jeffreyer/Bottle/src/text.cpp

#include "text.h"
#include <Arduino.h>
#include <stdio.h>
#include "common.h"
#include "esp_partition.h"

uint8_t text[] = {'H','e','l','l','o','1','2','3',0xCF, 0xC8, 0xB5, 0xDB, 0xB4, 0xB4, 0xD2, 0xB5, 0xCE, 0xB4, 0xB0, 0xEB, 0xB6, 0xF8, 0xD6, 0xD0, 0xB5, 0xC0, 0xB1, 0xC0, 0xE9, 0xE3, 0xA3, 0xAC, 0xBD, 0xF1, 0xCC, 0xEC, 0xCF, 0xC2, 0xC8, 0xFD, 0xB7, 0xD6, 0xA3, 0xAC, 0xD2, 0xE6, 0xD6, 0xDD, 0xC6, 0xA3, 0xB1, 0xD7, 0xA3, 0xAC, 0xB4, 0xCB, 0xB3, 0xCF, 0xCE, 0xA3, 0xBC, 0xB1, 0xB4, 0xE6, 0xCD, 0xF6, 0xD6, 0xAE, 0xC7, 0xEF, 0xD2, 0xB2, 0xA1, 0xA3, 0xC8, 0xBB, 0xCA, 0xCC, 0xCE, 0xC0, 0xD6, 0xAE, 0xB3, 0xBC, 0xB2, 0xBB, 0xD0, 0xB8, 0xD3, 0xDA, 0xC4, 0xDA, 0xA3, 0xAC, 0xD6, 0xD2, 0xD6, 0xBE, 0xD6, 0xAE, 0xCA, 0xBF, 0xCD, 0xFC, 0xC9, 0xED, 0xD3, 0xDA, 0xCD, 0xE2, 0xD5, 0xDF, 0xA3, 0xAC, 0xB8, 0xC7, 0xD7, 0xB7, 0xCF, 0xC8, 0xB5, 0xDB, 0xD6, 0xAE, 0xCA, 0xE2, 0xD3, 0xF6, 0xA3, 0xAC, 0xD3, 0xFB, 0xB1, 0xA8, 0xD6, 0xAE, 0xD3, 0xDA, 0xB1, 0xDD, 0xCF, 0xC2, 0xD2, 0xB2, 0xA1, 0xA3, 0xB3, 0xCF, 0xD2, 0xCB, 0xBF, 0xAA, 0xD5, 0xC5, 0xCA, 0xA5, 0xCC, 0xFD, 0xA3, 0xAC, 0xD2, 0xD4, 0xB9, 0xE2, 0xCF, 0xC8, 0xB5, 0xDB, 0xD2, 0xC5, 0xB5, 0xC2, 0xA3, 0xAC, 0xBB, 0xD6, 0xBA, 0xEB, 0xD6, 0xBE, 0xCA, 0xBF, 0xD6, 0xAE, 0xC6, 0xF8, 0xA3, 0xAC, 0xB2, 0xBB, 0xD2, 0xCB, 0xCD, 0xFD, 0xD7, 0xD4, 0xB7, 0xC6, 0xB1, 0xA1, 0xA3, 0xAC, 0xD2, 0xFD, 0xD3, 0xF7, 0xCA, 0xA7, 0xD2, 0xE5, 0xA3, 0xAC, 0xD2, 0xD4, 0xC8, 0xFB, 0xD6, 0xD2, 0xDA, 0xC9, 0xD6, 0xAE, 0xC2, 0xB7, 0xD2, 0xB2, 0xA1, 0xA3, 0x0A, 0xB9, 0xAC, 0xD6, 0xD0, 0xB8, 0xAE, 0xD6, 0xD0, 0xA3, 0xAC, 0xBE, 0xE3, 0xCE, 0xAA, 0xD2, 0xBB, 0xCC, 0xE5, 0xA3, 0xBB, 0xDA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
int text_index=0;
bool single_finish=true;
uint8_t *last_glyph;

int gb2312_to_index(uint8_t high, uint8_t low)
{
    if (high==0)
        return low-0x20;
    if (high >= 0xB0 && high <= 0xD7) {
        return (high - 0xB0) * 94 + (low - 0xA1) + 95;
    }
    if (high >= 0xD8 && high <= 0xF7) {
        return (high - 0xD8 + 40) * 94 + (low - 0xA1) + 95;
    }
    return -1;
}

#define FONT_BASE_ADDR 0x390000
#define FONT_PAGE_SIZE (256 * 8)   // 256字/页 × 8 bytes
#define PAGE_CHAR_COUNT 256

typedef struct {
    uint16_t page_id;
    uint8_t data[PAGE_CHAR_COUNT * 8];
    bool valid;
} font_page_t;

font_page_t cache[2];  // 双页缓存

const esp_partition_t* font_part;

void init_font_partition()
{
    font_part = esp_partition_find_first(
        ESP_PARTITION_TYPE_DATA,
        ESP_PARTITION_SUBTYPE_ANY,
        "font"
    );

    if (!font_part) {
        Serial.println("Font partition not found!");
    }
}

bool font_read(uint32_t offset, void* buffer, uint32_t len)
{
    if (!font_part) return false;

    esp_err_t err = esp_partition_read(
        font_part,
        offset,
        buffer,
        len
    );

    return err == ESP_OK;
}

void load_page(uint16_t page_id)
{
    // 查缓存
    for (int i = 0; i < 2; i++) {
        if (cache[i].valid && cache[i].page_id == page_id) return;
    }

    // 替换策略（简单LRU）
    int slot = 0;
    cache[slot].page_id = page_id;
    cache[slot].valid = true;

    // uint32_t addr = FONT_BASE_ADDR + page_id * FONT_PAGE_SIZE;

    // spi_flash_read(addr, cache[slot].data, FONT_PAGE_SIZE);

    uint32_t offset = page_id * FONT_PAGE_SIZE;
    font_read(offset, cache[slot].data, FONT_PAGE_SIZE);
}

uint8_t* get_glyph(uint16_t index)
{
    uint16_t page = index / PAGE_CHAR_COUNT;
    uint16_t offset = index % PAGE_CHAR_COUNT;

    load_page(page);

    for (int i = 0; i < 2; i++) {
        if (cache[i].page_id == page) {
            return &cache[i].data[offset * 8];
        }
    }

    return NULL;
}

void push_space(int space){
    // int space = 2;  // 间距列数（推荐 1~3）

    for (int s = 0; s < space; s++) {

        // 左移
        for (int x = 0; x < MATRIX_WIDTH - 1; x++) {
            for (int y = 0; y < MATRIX_HEIGHT; y++) {
                leds(x, y) = leds(x + 1, y);
            }
        }

        // 写入空列（全黑）
        int x = MATRIX_WIDTH - 1;
        for (int y = 0; y < MATRIX_HEIGHT; y++) {
            leds(x, y) = CRGB::Black;
        }

        FastLED.show();
        delay(100);
    }
}

int col=0;
void push_char(uint8_t *glyph)
{
    // 每个字符 8列
    // for (int col = 0; col < 8; col++) {

        // ===== 1. 整体左移一列 =====
        for (int x = 0; x < MATRIX_WIDTH - 1; x++) {
            for (int y = 0; y < MATRIX_HEIGHT; y++) {

                leds(x, y) = leds(x + 1, y);

            }
        }

        // ===== 2. 最右侧写入新列 =====
        int x = MATRIX_WIDTH - 1;

        for (int y = 0; y < 8 && y < MATRIX_HEIGHT; y++) {

            // uint8_t row = glyph[y];

            // 取当前列 bit
            // bool pixel = (row >> (7 - col)) & 0x01;
            bool pixel = (glyph[7 - y] >> (7 - col)) & 1;

            leds(x, y) = pixel ? CRGB(100,100,100) : CRGB::Black;
        }

        // ===== 3. 显示 =====
        FastLED.show();

        delay(100); // 滚动速度
    // }
    
    
}

void text_loop()
{
    if (!single_finish){
        push_char(last_glyph);
        col++;
        if (col==8){
            single_finish=true;
            col=0;
            push_space(1);
        }
        return;
    }

    delay(20);
    
    int len=sizeof(text);
    int i=text_index;
    // for (int i = 0; i < len; )
    // {
        if (text[i] < 0x80) {
            int idx = gb2312_to_index(0,text[i]);
            uint8_t* glyph = get_glyph(idx);

            if (glyph) {
                push_char(glyph);
            }
           
            i += 1;
            text_index+=1;
        }
        else {
            // ===== 中文（GB2312）=====
            if (i + 1 >= len){
                text_index=0;
                push_space(6);
                return;
            }

            uint8_t h = text[i];
            uint8_t l = text[i + 1];

            int idx = gb2312_to_index(h, l);
            uint8_t* glyph = get_glyph(idx);

            if (glyph) {
                single_finish=false;
                last_glyph=glyph;
                // push_char(glyph);
                
            }

            i += 2;
            text_index+=2;
        }
    // }

    // push_space(6);
}

int setup_text(){
    if (is_led)
        brightness_max=(int)(user_brightness_max/2+2);
    else
        brightness_max = user_brightness_max;
    FastLED.setBrightness(brightness_max);
    
    init_font_partition();
    
    return 0;

}

int unload_text(){
    return 0;
}
