jeffreyer/Bottle/src/rgb.h

#ifndef __RGB_H_
#define __RGB_H_
#include <stdint.h>

void rgb_init(void);
void rgb_deinit(void);
void rgb_set(uint8_t x, uint8_t y, uint8_t r, uint8_t g, uint8_t b);
void rgb_set_fast(uint32_t index, uint8_t r, uint8_t g, uint8_t b);
void rgb_clear(void);
void rgb_set_hsv(uint32_t index, uint16_t hue, uint16_t light);
void rgb_show(void);
void rgb_set_brightness(uint8_t brightness);
uint8_t rgb_get_brightness(void);

#endif // !__RGB_H_
